mwicat/tiny_iambic_keyer/docs/kicad/morse_decoder/morse_decoder.kicad_sch

## KiCad design docs/kicad/morse_decoder/morse_decoder.kicad_sch (2023-02-09)

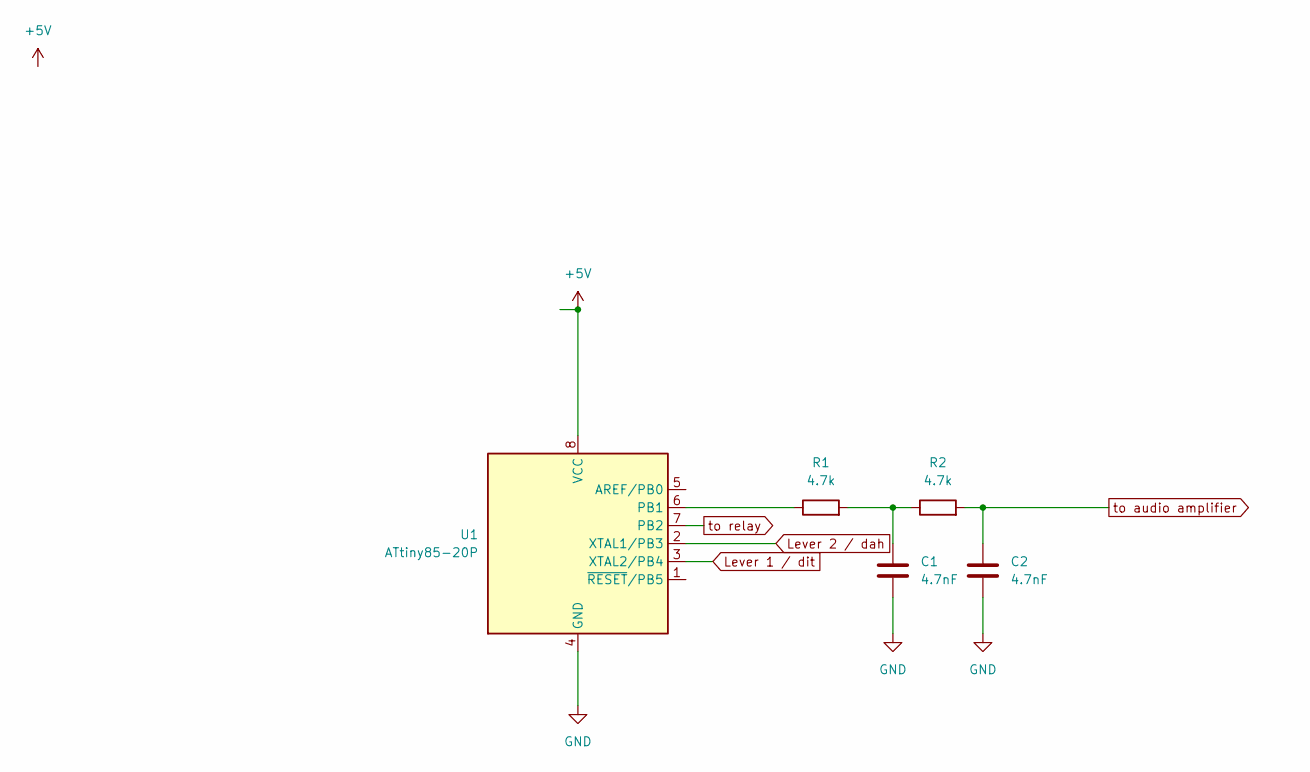
[picture p4: schematic morse_decoder.kicad_sch]

Parts:
C1, C2: 4.7nF
R1, R2: 4.7k
U1: ATtiny85-20P; DIP-8_W7.62mm

Connections:
+5V: U1.8 (VCC)
GND: C1.2, C2.2, U1.4 (GND)
Lever 1 / dit: U1.3 (XTAL2/PB4)
Lever 2 / dah: U1.2 (XTAL1/PB3)
unnamed: C1.1, R1.2, R2.1
unnamed: R1.1, U1.6 (PB1)
to audio amplifier: C2.1, R2.2
to relay: U1.7 (PB2)
